accretio/wingleveler/case/stl/right_rail.stl

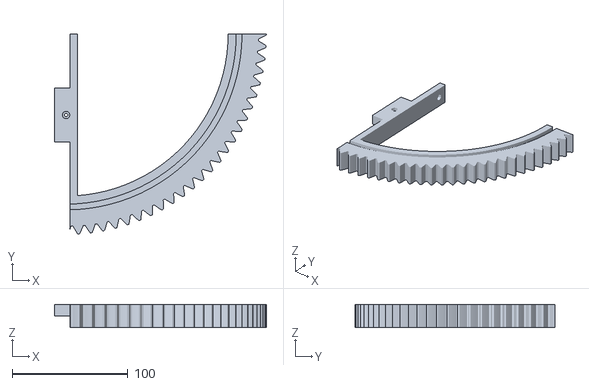
[picture p18: CAD file, 2016-10-28]
case/stl/right_rail.stl
183.2 x 172.9 x 20.0
