accretio/wingleveler/case/stl/rail.stl

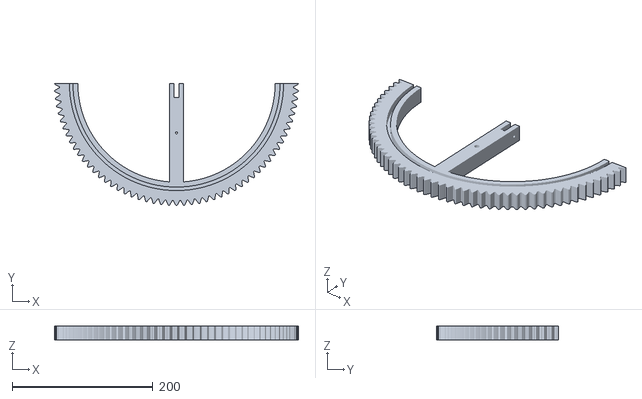
[picture p19: CAD file, 2016-10-22]
case/stl/rail.stl
346.3 x 173.2 x 20.0
