accretio/wingleveler/case/stl/mount.stl

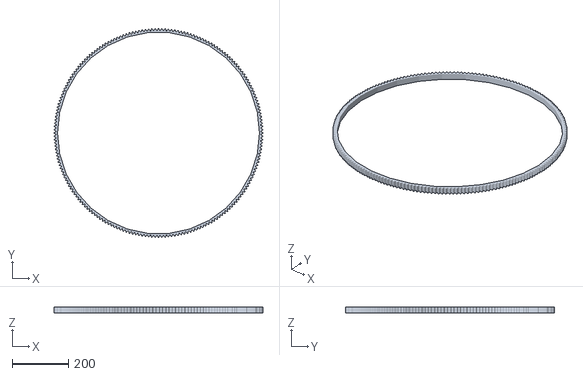
[picture p20: CAD file, 2016-10-19]
case/stl/mount.stl
745.1 x 745.1 x 20.0
