accretio/wingleveler/case/src/front_controller.scad

use <controller.scad>

controller_front_plate();
