accretio/wingleveler/case/src/left_rail.scad

use <rail.scad>

left_rail();
