accretio/wingleveler/case/src/right_rail.scad

use <rail.scad>

right_rail();
