accretio/wingleveler/case/src/screw.scad

include <clamp.scad>

big_screw();
