accretio/wingleveler/driver/quaternion.c

////////////////////////////////////////////////////////////////////////////
//
//  This file is part of linux-mpu9150
//
//  Copyright (c) 2013 Pansenti, LLC
//
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
#include "quaternion.h"

void quaternionNorm(quaternion_t q, float *n)
{
	*n = sqrtf(q[QUAT_W] * q[QUAT_W] + q[QUAT_X] * q[QUAT_X] +  
				q[QUAT_Y] * q[QUAT_Y] + q[QUAT_Z] * q[QUAT_Z]);
}

void quaternionNormalize(quaternion_t q)
{
	float length;

	quaternionNorm(q, &length);

	if (length == 0)
		return;

	q[QUAT_W] /= length;
	q[QUAT_X] /= length;
	q[QUAT_Y] /= length;
	q[QUAT_Z] /= length;
}

void quaternionToEuler(quaternion_t q, vector3d_t v)
{
	// fix roll near poles with this tolerance
	float pole = (float)M_PI / 2.0f - 0.05f;

	v[VEC3_Y] = asinf(2.0f * (q[QUAT_W] * q[QUAT_Y] - q[QUAT_X] * q[QUAT_Z]));

	if ((v[VEC3_Y] < pole) && (v[VEC3_Y] > -pole)) {
		v[VEC3_X] = atan2f(2.0f * (q[QUAT_Y] * q[QUAT_Z] + q[QUAT_W] * q[QUAT_X]),
					1.0f - 2.0f * (q[QUAT_X] * q[QUAT_X] + q[QUAT_Y] * q[QUAT_Y]));
	}

	v[VEC3_Z] = atan2f(2.0f * (q[QUAT_X] * q[QUAT_Y] + q[QUAT_W] * q[QUAT_Z]),
					1.0f - 2.0f * (q[QUAT_Y] * q[QUAT_Y] + q[QUAT_Z] * q[QUAT_Z]));
}

void eulerToQuaternion(vector3d_t v, quaternion_t q)
{
	float cosX2 = cosf(v[VEC3_X] / 2.0f);
	float sinX2 = sinf(v[VEC3_X] / 2.0f);
	float cosY2 = cosf(v[VEC3_Y] / 2.0f);
	float sinY2 = sinf(v[VEC3_Y] / 2.0f);
	float cosZ2 = cosf(v[VEC3_Z] / 2.0f);
	float sinZ2 = sinf(v[VEC3_Z] / 2.0f);

	q[QUAT_W] = cosX2 * cosY2 * cosZ2 + sinX2 * sinY2 * sinZ2;
	q[QUAT_X] = sinX2 * cosY2 * cosZ2 - cosX2 * sinY2 * sinZ2;
	q[QUAT_Y] = cosX2 * sinY2 * cosZ2 + sinX2 * cosY2 * sinZ2;
	q[QUAT_Z] = cosX2 * cosY2 * sinZ2 - sinX2 * sinY2 * cosZ2;

	quaternionNormalize(q);
}

void quaternionConjugate(quaternion_t s, quaternion_t d) 
{
	d[QUAT_W] = s[QUAT_W];
	d[QUAT_X] = -s[QUAT_X];
	d[QUAT_Y] = -s[QUAT_Y];
	d[QUAT_Z] = -s[QUAT_Z];
}
	
void quaternionMultiply(quaternion_t qa, quaternion_t qb, quaternion_t qd) 
{
	vector3d_t va;
	vector3d_t vb;
	float dotAB;
	vector3d_t crossAB;
	
	va[VEC3_X] = qa[QUAT_X];
	va[VEC3_Y] = qa[QUAT_Y];
	va[VEC3_Z] = qa[QUAT_Z];

	vb[VEC3_X] = qb[QUAT_X];
	vb[VEC3_Y] = qb[QUAT_Y];
	vb[VEC3_Z] = qb[QUAT_Z];

	vector3DotProduct(va, vb, &dotAB);
	vector3CrossProduct(va, vb, crossAB);
	
	qd[QUAT_W] = qa[QUAT_W] * qb[QUAT_W] - dotAB;
	qd[QUAT_X] = qa[QUAT_W] * vb[VEC3_X] + qb[QUAT_W] * va[VEC3_X] + crossAB[VEC3_X];
	qd[QUAT_Y] = qa[QUAT_W] * vb[VEC3_Y] + qb[QUAT_W] * va[VEC3_Y] + crossAB[VEC3_Y];
	qd[QUAT_Z] = qa[QUAT_W] * vb[VEC3_Z] + qb[QUAT_W] * va[VEC3_Z] + crossAB[VEC3_Z];
}
