accretio/wingleveler/driver/automated.c

// automated control of the weight

#include <stdio.h>
#include <stdlib.h>
#include <signal.h>
#include <pthread.h>
#include <math.h>

#include "utils.h"
#include "config.h"
#include "state.h"
#include "control.h"
#include "servo.h"
#include "ahrs.h"
#include "linux_glue.h"

int automated_loop(struct state_t *state)
{
  int rc;
  
  refresh_ahrs(state);
  linux_delay_ms(WARMING_DELAY);
  refresh_ahrs(state);
  state->bank_reference=state->bank;

  if (rc = start_servo(state)) {
    return rc;
  }
  
  while(!kbhit()) {
    refresh_ahrs(state);
    printf("current bank: %f, current bank rate: %f, current action: %d\n",
           state->bank,
           state->bank_delta,
           state->action);

    if (fabs(state->bank) < BANK_TOLERANCE) {
      state->action = DONT_MOVE;
    } else {
      // let's target a bank_delta of -state->bank
      float target = - BANK_CORRECTION_FACTOR * state->bank;
      printf("target is %f\n", target);
      if (state->bank < 0) {
        if (state->bank_delta > target) {
          state->action = MOVE_RIGHT; 
        } else {
          state->action = MOVE_LEFT;
        }
      } else {
        if (state->bank_delta < target) {
          state->action = MOVE_LEFT; 
        } else {
          state->action = MOVE_RIGHT;
        }
      }
      
      pthread_cond_signal(&cond);
    }
    
    linux_delay_ms(135); 
  }

  return 0;
}
