accretio/wingleveler/driver/utils.c

#include <sys/select.h>
#include <time.h>

int kbhit()
{
  struct timeval tv;
  fd_set fds;
  tv.tv_sec = 0;
  tv.tv_usec = 0;
  FD_ZERO(&fds);
#define STDIN_FILENO 0
  FD_SET(STDIN_FILENO, &fds); //STDIN_FILENO is 0
  select(STDIN_FILENO+1, &fds, NULL, NULL, &tv);
  return FD_ISSET(STDIN_FILENO, &fds);
}
